roelvndobelen/BMO-Desk-Companion/3d-prints/originals/buttontriangle_bmo.stl

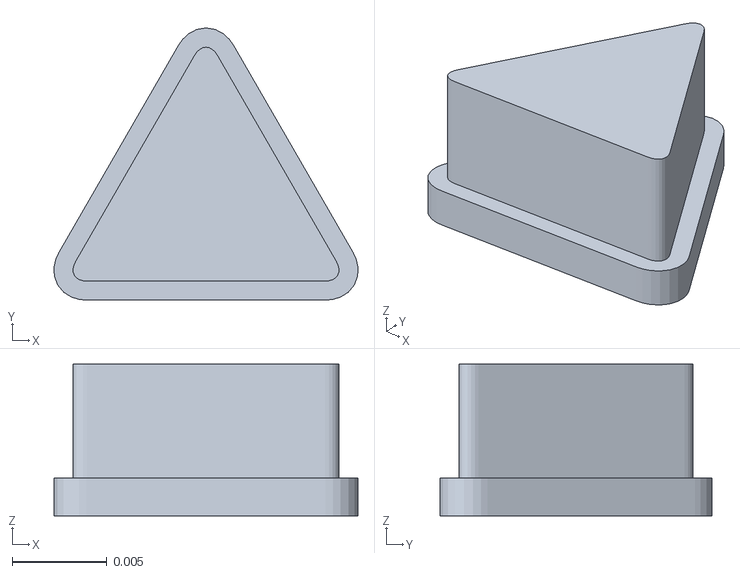
[picture p15: CAD file, 2026-09-21]
3d-prints/originals/buttontriangle_bmo.stl
0.016 x 0.0143 x 0.008
