roelvndobelen/BMO-Desk-Companion/3d-prints/originals/buttoncircle_bmo.stl

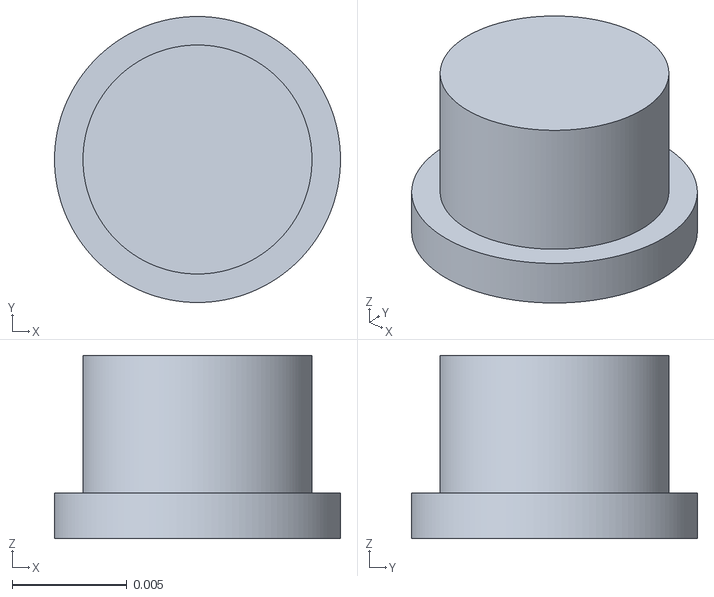
[picture p16: CAD file, 2026-09-21]
3d-prints/originals/buttoncircle_bmo.stl
0.0125 x 0.0125 x 0.008
