roelvndobelen/BMO-Desk-Companion/3d-prints/originals/arms_bmo.stl

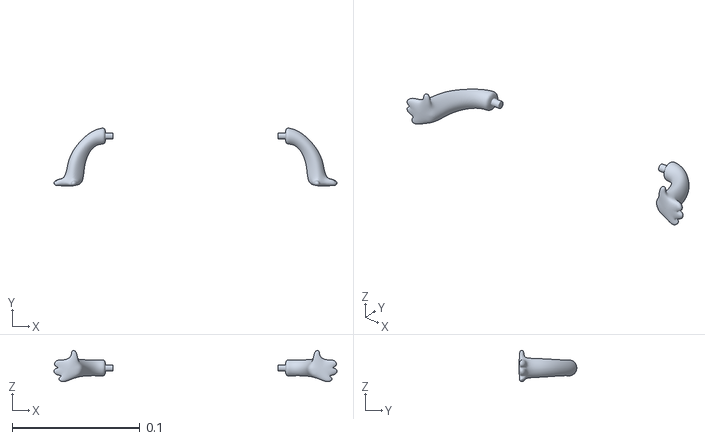
[picture p17: CAD file, 2026-09-21]
3d-prints/originals/arms_bmo.stl
0.221 x 0.0451 x 0.0245
