roelvndobelen/BMO-Desk-Companion/3d-prints/originals/buttonbigcircle_bmo.stl

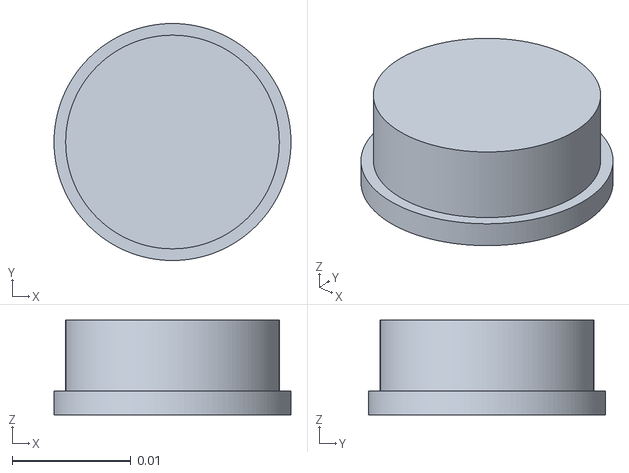
[picture p18: CAD file, 2026-09-21]
3d-prints/originals/buttonbigcircle_bmo.stl
0.02 x 0.02 x 0.008
